MartinNohr/RadioFox/src/FoxMenus.cpp

#include "RadioFox.h"
#include "FoxMenus.h"

// do something from the menu depending on the button argument
// only two buttons are actually handled, SELECT and HELP
void RunMenus(int button)
{
    // see if we got a menu match
    bool gotmatch = false;
    int menuix = 0;
    MenuInfo *oldMenu;
    bool bExit = false;
    for (int ix = 0; !gotmatch && MenuStack.top()->menu[ix].op != eTerminate; ++ix)
    {
        // see if this is one is valid
        if (!bMenuValid[ix])
        {
            continue; // and don't increment menix
        }
        if (menuix == MenuStack.top()->index)
        {
            gotmatch = true;
            switch (button)
            {
            case BTN_B1_LONG: // handle help if there is any
                if (MenuStack.top()->menu[ix].cHelpText)
                {
                    WriteMessage(MenuStack.top()->menu[ix].cHelpText, false, -1, true);
                }
                g_bMenuChanged = true;
                break;
            case BTN_SELECT: // handle selection
                // got one, service it
                switch (MenuStack.top()->menu[ix].op)
                {
                case eTerminate: // not used, tell compiler
                case eIfEqual:
                case eIfIntEqual:
                case eElse:
                case eEndif:
                    break;
                case eText:
                case eTextInt:
                case eTextFloat:
                case eEditText:
                // case eChooseFile:
                case eBool:
                case eList:
                    g_bMenuChanged = true;
                    if (MenuStack.top()->menu[ix].change != NULL)
                    {
                        (*MenuStack.top()->menu[ix].change)(&MenuStack.top()->menu[ix], 1);
                    }
                    if (MenuStack.top()->menu[ix].function)
                    {
                        (*MenuStack.top()->menu[ix].function)(&MenuStack.top()->menu[ix]);
                    }
                    if (MenuStack.top()->menu[ix].change != NULL)
                    {
                        (*MenuStack.top()->menu[ix].change)(&MenuStack.top()->menu[ix], -1);
                    }
                    break;
                case eMenu:
                    if (MenuStack.top()->menu)
                    {
                        oldMenu = MenuStack.top();
                        MenuStack.push(new MenuInfo);
                        MenuStack.top()->menu = oldMenu->menu[ix].menu;
                        g_bMenuChanged = true;
                        MenuStack.top()->index = 0;
                        MenuStack.top()->offset = 0;
                        // Serial.println("change menu");
                    }
                    break;
                case eExit: // go back a level
                    bExit = true;
                    break;
                case eReboot:
                    WriteMessage("Rebooting in 2 seconds\nHold button for factory reset", false, 2000);
                    ESP.restart();
                    break;
                }
            }
        }
        ++menuix;
    }
    // if no match, and we are in a submenu, go back one level, or if bExit is set
    if (bExit && MenuStack.size() == 1)
    {
        g_bSettingsMode = false;
        ClearScreen();
    }
    if (bExit || (!g_bMenuChanged && MenuStack.size() > 1))
    {
        UpMenuLevel(false);
    }
}

// display the menu
// if MenuStack.top()->index is > MENU_LINES, then shift the lines up by enough to display them
// remember that we only have room for MENU_LINES lines
void ShowMenu(struct MenuItem *menu)
{
    // let the sideways scroller know that we changed the screen
    if (TaskScrollSidewaysHandle)
        xTaskNotifyGive(TaskScrollSidewaysHandle);
    MenuStack.top()->menucount = 0;
    int y = 0;
    int x = 0;
    // load with a false to start with
    std::stack<bool> skipStack;
    skipStack.push(false);
    // this is the active stack level, I.E. which level should be processed
    int skipLevel = 1;
    bool bSkipping = false;
    // loop through the menu
    for (int menix = 0; menu->op != eTerminate; ++menu, ++menix)
    {
        // make sure menu valid vector is big enough
        if (bMenuValid.size() < menix + 1)
        {
            bMenuValid.resize(menix + 1);
        }
        bMenuValid[menix] = false;
        switch ((menu->op))
        {
        case eIfEqual:
            // skip the next one if match, this is boolean only
            skipStack.push(*(bool *)menu->value != (menu->min ? true : false));
            // Serial.println("ifequal test: skip: " + String(skip));
            if (!bSkipping)
            {
                ++skipLevel;
                bSkipping = skipStack.top();
            }
            break;
        case eIfIntEqual:
            // skip the next one if match, this is int values
            skipStack.push(*(int *)menu->value != menu->min);
            // Serial.println("ifIntequal test: skip: " + String(skip));
            if (!bSkipping)
            {
                ++skipLevel;
                bSkipping = skipStack.top();
            }
            break;
        case eElse:
            skipStack.top() = !skipStack.top();
            break;
        case eEndif:
            skipStack.pop();
            if (!bSkipping || skipLevel > skipStack.size())
            {
                --skipLevel;
            }
            break;
        default:
            break;
        }
        bSkipping = skipLevel < skipStack.size() ? true : skipStack.top();
        if (bSkipping)
        {
            bMenuValid[menix] = false;
            continue;
        }
        char line[120]{}, xtraline[100]{};
        // only displayable menu items should be in this switch
        line[0] = '\0';
        int val;
        bool exists = false;
        switch (menu->op)
        {
        case eTextInt:
        case eTextFloat:
        case eText:
        case eEditText:
            // case eChooseFile:
            bMenuValid[menix] = true;
            if (menu->value)
            {
                val = *(int *)menu->value;
                if (menu->op == eText || menu->op == eEditText /*|| menu->op == eChooseFile*/)
                {
                    sprintf(line, menu->text, (char *)(menu->value));
                }
                else if (menu->op == eTextInt)
                {
                    sprintf(line, menu->text, (int)(val / pow10(menu->decimals)), val % (int)(pow10(menu->decimals)));
                }
                else if (menu->op == eTextFloat)
                {
                    double fval = *(double *)menu->value;
                    sprintf(line, menu->text, fval);
                }
            }
            else
            {
                strcpy(line, menu->text);
            }
            // next line
            ++y;
            break;
        case eList:
            bMenuValid[menix] = true;
            val = *(int *)menu->value;
            sprintf(line, menu->text, menu->nameList[val]);
            // next line
            ++y;
            break;
        case eBool:
            bMenuValid[menix] = true;
            if (menu->value)
            {
                bool *pb = (bool *)menu->value;
                sprintf(line, menu->text, *pb ? menu->on : menu->off);
            }
            else
            {
                strcpy(line, menu->text);
            }
            // increment displayable lines
            ++y;
            break;
        case eMenu:
        case eExit:
        case eReboot:
            bMenuValid[menix] = true;
            if (menu->value)
            {
                // check for %d or %s in string, be lazy and assume %s if %d not there
                if (String(menu->text).indexOf("%d") != -1)
                    sprintf(xtraline, menu->text, *(int *)menu->value);
                else
                    sprintf(xtraline, menu->text, (char *)menu->value);
            }
            else
            {
                strcpy(xtraline, menu->text);
            }
            if (menu->op == eExit)
                sprintf(line, "%s%s", "-", xtraline);
            else
                sprintf(line, "%s%s", (menu->op == eReboot) ? "" : "+", xtraline);
            ++y;
            // Serial.println("menu text4: " + String(line));
            break;
        default:
            break;
        }
        if (strlen(line) && y >= MenuStack.top()->offset)
        {
            DisplayMenuLine(y - 1, y - 1 - MenuStack.top()->offset, line);
        }
    }
    MenuStack.top()->menucount = y;
    // blank the rest of the lines
    for (int ix = y; ix < nMenuLineCount; ++ix)
    {
        DisplayLine(ix, "");
    }
    // show line if menu has been scrolled
    if (MenuStack.top()->offset > 0)
        tft.fillTriangle(0, 0, 2, 0, 0, tft.fontHeight() / 3, TFT_DARKGREY);
    // tft.drawLine(0, 0, 5, 0, menuLineActiveColor);TFT_DARKGREY
    // show bottom line if last line is showing
    if (MenuStack.top()->offset + (nMenuLineCount - 1) < MenuStack.top()->menucount - 1)
    {
        int ypos = tft.height() - 2 - tft.fontHeight() / 3;
        tft.fillTriangle(0, ypos, 2, ypos, 0, ypos - tft.fontHeight() / 3, TFT_DARKGREY);
    }
    // if (MenuStack.top()->offset + (MENU_LINES - 1) < MenuStack.top()->menucount - 1)
    //	tft.drawLine(0, tft.height() - 1, 5, tft.height() - 1, menuLineActiveColor);
    // else
    //	tft.drawLine(0, tft.height() - 1, 5, tft.height() - 1, TFT_BLACK);
    //  see if we need to clean up the end, like when the menu shrank due to a choice
    int extra = MenuStack.top()->menucount - MenuStack.top()->offset - nMenuLineCount;
    while (extra < 0)
    {
        DisplayLine(nMenuLineCount + extra, "");
        ++extra;
    }
}

// handle the menus
bool HandleMenus()
{
    if (g_bMenuChanged)
    {
        ShowMenu(MenuStack.top()->menu);
        g_bMenuChanged = false;
    }
    bool didsomething = true;
    CRotaryDialButton::Button button = ReadButton();
    int lastOffset = MenuStack.top()->offset;
    int lastMenu = MenuStack.top()->index;
    int lastMenuCount = MenuStack.top()->menucount;
    // MenuItem* pCurrentMenu = &MenuStack.top()->menu[MenuStack.top()->index];
    int btnRepeatCount = 1;
    switch (button)
    {
    case BTN_LEFT_LONG:
    case BTN_RIGHT_LONG:
        btnRepeatCount = 5;
        break;
    }
    switch (button)
    {
    case BTN_B0_CLICK: // go back a menu level if we can
        UpMenuLevel(false);
        break;
    case BTN_B1_LONG: // look for help
        // UpMenuLevel(true);	// go back to the top menu
        RunMenus(button);
        g_bMenuChanged = true;
        break;
    // case BTN_B1_LONG:
    //	button = BTN_SELECT;
    //  yes, no break here
    case BTN_SELECT:
        RunMenus(button);
        g_bMenuChanged = true;
        break;
    case BTN_RIGHT_LONG:
    case BTN_RIGHT:
        while (btnRepeatCount--)
        {
            if (SystemInfo.bAllowMenuWrap || MenuStack.top()->index < MenuStack.top()->menucount - 1)
            {
                ++MenuStack.top()->index;
            }
            if (MenuStack.top()->index >= MenuStack.top()->menucount)
            {
                MenuStack.top()->index = 0;
                g_bMenuChanged = true;
                MenuStack.top()->offset = 0;
            }
            // see if we need to scroll the menu
            if (MenuStack.top()->index - MenuStack.top()->offset > (nMenuLineCount - 1))
            {
                if (MenuStack.top()->offset < MenuStack.top()->menucount - nMenuLineCount)
                {
                    ++MenuStack.top()->offset;
                }
            }
        }
        break;
    case BTN_LEFT_LONG:
    case BTN_LEFT:
        while (btnRepeatCount--)
        {
            if (SystemInfo.bAllowMenuWrap || MenuStack.top()->index > 0)
            {
                --MenuStack.top()->index;
            }
            if (MenuStack.top()->index < 0)
            {
                MenuStack.top()->index = MenuStack.top()->menucount - 1;
                g_bMenuChanged = true;
                MenuStack.top()->offset = MenuStack.top()->menucount - nMenuLineCount;
            }
            // see if we need to adjust the offset
            if (MenuStack.top()->offset && MenuStack.top()->index < MenuStack.top()->offset)
            {
                --MenuStack.top()->offset;
            }
        }
        break;
    case BTN_LONG:
        ClearScreen();
        g_bSettingsMode = false;
        g_bMenuChanged = true;
        break;
    default:
        didsomething = false;
        break;
    }
    // check some conditions that should redraw the menu
    if (lastMenu != MenuStack.top()->index || lastOffset != MenuStack.top()->offset)
    {
        g_bMenuChanged = true;
        // Serial.println("menu changed");
    }
    return didsomething;
}

// handle keys in run mode
bool HandleRunMode()
{
    bool didsomething = true;
    int maxMenuLine = nMenuLineCount - (SystemInfo.bShowBatteryLevel ? 2 : 1);
    CRotaryDialButton::Button button = ReadButton();
    switch (button)
    {
    case BTN_SELECT:
        break;
    case BTN_RIGHT_LONG:
    case BTN_RIGHT:
        break;
    case BTN_LEFT_LONG:
    case BTN_LEFT:
        break;
    case BTN_LONG:
        g_bSettingsMode = true;
        break;
    case BTN_B0_CLICK:
        // handle on board button 0
        // toggle the run flag
        SystemInfo.bXmitEnable = !SystemInfo.bXmitEnable;
        RadioSetup(false);
        break;
    case BTN_B0_LONG:
        CancelWaitTimers(NULL);
        break;
    case BTN_B1_CLICK:
        break;
    case BTN_B1_LONG:
    case BTN_LEFT_RIGHT_LONG:
        break;
    default:
        didsomething = false;
        taskYIELD();
        break;
    }
    return didsomething;
}

// go up one menu level, return true if anything done
// set gotoMain to go all the way back to the top
bool UpMenuLevel(bool gotoMain)
{
    if (gotoMain)
    {
        while (UpMenuLevel(false))
            ;
    }
    else if (MenuStack.size() > 1)
    {
        g_bMenuChanged = true;
        menuPtr = MenuStack.top();
        MenuStack.pop();
        delete menuPtr;
        return true;
    }
    return false;
}

uint16_t ColorList[] = {
    // TFT_NAVY,
    // TFT_MAROON,
    // TFT_OLIVE,
    TFT_WHITE,
    TFT_LIGHTGREY,
    TFT_BLUE,
    TFT_SKYBLUE,
    TFT_CYAN,
    TFT_RED,
    TFT_BROWN,
    TFT_GREEN,
    TFT_MAGENTA,
    TFT_YELLOW,
    TFT_ORANGE,
    TFT_GREENYELLOW,
    TFT_GOLD,
    TFT_SILVER,
    TFT_VIOLET,
    TFT_PURPLE,
};

// find the color in the list
int FindMenuColor(uint16_t col)
{
    int ix;
    int colors = sizeof(ColorList) / sizeof(*ColorList);
    for (ix = 0; ix < colors; ++ix)
    {
        if (col == ColorList[ix])
            break;
    }
    return constrain(ix, 0, colors - 1);
}

void SetMenuColor(MenuItem *menu)
{
    bool bHiLiteColor = false;
    int maxIndex = sizeof(ColorList) / sizeof(*ColorList) - 1;
    int nTextColorIndex = FindMenuColor(SystemInfo.menuTextColor);
    int nHiLiteColorIndex = FindMenuColor(SystemInfo.menuHiLiteColor);
    int nSavedTextColorIndex = nTextColorIndex;
    int nSavedHiLiteColorIndex = nHiLiteColorIndex;
    ClearScreen();
    DisplayLine(3, "Rotate change value", SystemInfo.menuTextColor);
    DisplayLine(5, "Long B0 reset", SystemInfo.menuTextColor);
    DisplayLine(6, "Long=OK Click=Cancel", SystemInfo.menuTextColor);
    bool done = false;
    bool bChanged = true;
    int *npColor;
    String prefix0, prefix1;
    while (!done)
    {
        npColor = bHiLiteColor ? &nHiLiteColorIndex : &nTextColorIndex;
        if (bChanged)
        {
            if (bHiLiteColor)
            {
                prefix0 = "     ";
                prefix1 = "--> ";
            }
            else
            {
                prefix0 = "--> ";
                prefix1 = "     ";
            }
            DisplayLine(4, String("B0 Change to ") + (bHiLiteColor ? "Text" : "HiLite"), ColorList[nSavedTextColorIndex]);
            DisplayLine(0, prefix0 + "Text Color", SystemInfo.menuTextColor);
            DisplayLine(1, prefix1 + "HiLite Color", TFT_BLACK, SystemInfo.menuHiLiteColor);
            bChanged = false;
        }
        switch (ReadButton())
        {
        case CRotaryDialButton::BTN_LONGPRESS:
            done = true;
            break;
        case CRotaryDialButton::BTN_RIGHT:
            bChanged = true;
            if (*npColor < maxIndex)
            {
                ++(*npColor);
            }
            break;
        case CRotaryDialButton::BTN_LEFT:
            bChanged = true;
            if (*npColor > 0)
            {
                --(*npColor);
            }
            break;
        case CRotaryDialButton::BTN0_CLICK:
            bChanged = true;
            bHiLiteColor = !bHiLiteColor;
            break;
        case CRotaryDialButton::BTN0_LONGPRESS:
            nHiLiteColorIndex = nSavedHiLiteColorIndex;
            nTextColorIndex = nSavedTextColorIndex;
            bChanged = true;
            break;
        case CRotaryDialButton::BTN_CLICK:
            nHiLiteColorIndex = nSavedHiLiteColorIndex;
            nTextColorIndex = nSavedTextColorIndex;
            done = true;
            break;
        }
        SystemInfo.menuTextColor = ColorList[nTextColorIndex];
        SystemInfo.menuHiLiteColor = ColorList[nHiLiteColorIndex];
    }
}

// toggle a boolean value
void ToggleBool(MenuItem *menu)
{
    bool *pb = (bool *)menu->value;
    *pb = !*pb;
    if (menu->change != NULL)
    {
        (*menu->change)(menu, 0);
    }
    ResetTextLines();
}

// choose from one of the values, update the index and wrap around if past max
void GetSelectChoice(MenuItem *menu)
{
    int *pVal = (int *)menu->value;
    ++*pVal;
    *pVal %= menu->max + 1;
    if (menu->change != NULL)
    {
        (*menu->change)(menu, 0);
    }
    ResetTextLines();
}

// make a selection from the supplied text list in the menu
void GetSelectChoiceList(MenuItem *menu)
{
    GetSelectChoiceListHelper(menu);
}

// some people need to know if this was a cancel (simple click) return but function must be void
// return false if click for no choice, true if chosen
bool GetSelectChoiceListHelper(MenuItem *menu)
{
    bool bRetval = true;
    // holds the current selection
    int nTextIndex = *(int *)menu->value;
    int nOriginal = nTextIndex;
    // just to be safe
    if (nTextIndex < 0)
        nTextIndex = 0;
    // holds the list starting index
    int nStartIndex = nTextIndex;
    // see if we need adjust the start
    if (nTextIndex >= nMenuLineCount - 1)
    {
        nStartIndex = nTextIndex - nMenuLineCount + 2;
    }
    ClearScreen();
    DisplayLine(nMenuLineCount - 1, "Long=OK Click=Cancel", SystemInfo.menuTextColor);
    CRotaryDialButton::Button button = BTN_NONE;
    bool done = false;
    // redraw screen only when necessary
    bool bRedraw = true;
    do
    {
        if (bRedraw)
        {
            String line;
            bool hilite;
            for (int ix = 0; ix <= menu->max && ix < nMenuLineCount - 1; ++ix)
            {
                // high light the current selection
                hilite = (nTextIndex - nStartIndex) == ix;
                line = menu->nameList[ix + nStartIndex];
                if (SystemInfo.bMenuStar)
                {
                    line = (hilite ? "*" : " ") + line;
                    DisplayLine(ix, line, SystemInfo.menuTextColor);
                }
                else
                {
                    DisplayLine(ix, line, hilite ? TFT_BLACK : SystemInfo.menuTextColor, hilite ? SystemInfo.menuHiLiteColor : TFT_BLACK);
                }
            }
            bRedraw = false;
        }
        button = ReadButton();
        switch (button)
        {
        case BTN_NONE:
        case BTN_B1_CLICK:
        case BTN_B2_LONG:
        case BTN_B1_LONG:
        case BTN_B0_CLICK:
        case BTN_B0_LONG:
            break;
        case BTN_LEFT: // previous line
            if (nTextIndex > 0)
            {
                // select the previous one
                --nTextIndex;
                // check if we need to scroll
                if (nTextIndex - nStartIndex < 0)
                {
                    --nStartIndex;
                }
                bRedraw = true;
            }
            break;
        case BTN_RIGHT: // next line
            // check if more available
            if (nTextIndex < menu->max)
            {
                ++nTextIndex;
                // check if we need to scroll
                if (nTextIndex - nStartIndex >= nMenuLineCount - 1)
                {
                    ++nStartIndex;
                }
                bRedraw = true;
            }
            break;
        case BTN_LONG: // set the new index
            *(int *)menu->value = nTextIndex;
            done = true;
            bRetval = true;
            break;
        case BTN_SELECT: // use this to cancel and return original value
            *(int *)menu->value = nOriginal;
            done = true;
            bRetval = false;
            break;
        }
    } while (!done);
    ResetTextLines();
    return bRetval;
}

// get integer values
void GetIntegerValue(MenuItem *menu)
{
    ClearScreen();
    // -1 means to reset to original
    int stepSize = 1;
    int originalValue = *(int *)menu->value;
    // Serial.println("int: " + String(menu->text) + String(*(int*)menu->value));
    char line[50];
    CRotaryDialButton::Button button = BTN_NONE;
    bool done = false;
    const char *fmt;
    if (menu->decimals)
    {
        static char fmtInfo[50];
        // String st = String("%ld.%0") + menu->decimals + "ld";
        sprintf(fmtInfo, "%%ld.%%0%dld", menu->decimals);
        fmt = fmtInfo;
    }
    else
    {
        fmt = "%ld";
    }
    char minstr[50], maxstr[50], valstr[50];
    sprintf(line, menu->text, *(int *)menu->value / (int)pow10(menu->decimals), *(int *)menu->value % (int)pow10(menu->decimals));
    DisplayLine(0, line, SystemInfo.menuTextColor);
    sprintf(minstr, fmt, menu->min / (int)pow10(menu->decimals), abs(menu->min % (int)pow10(menu->decimals)));
    sprintf(maxstr, fmt, menu->max / (int)pow10(menu->decimals), abs(menu->max % (int)pow10(menu->decimals)));
    DisplayLine(1, String(minstr) + " to " + String(maxstr), SystemInfo.menuTextColor);
    DisplayLine(5, "Long Press B0 to reset", SystemInfo.menuTextColor);
    DisplayLine(6, "Long Press to Accept", SystemInfo.menuTextColor);
    int oldVal = *(int *)menu->value;
    bool bChange = true;
    do
    {
        if (bChange)
        {
            // make sure within limits
            *(int *)menu->value = constrain(*(int *)menu->value, menu->min, menu->max);
            // show slider bar
            tft.fillRect(0, 2 * tft.fontHeight(), tft.width() - 1, 6, TFT_BLACK);
            DrawProgressBar(0, 2 * tft.fontHeight() + 4, tft.width() - 1, 12, map(*(int *)menu->value, menu->min, menu->max, 0, 100), true);
            sprintf(valstr, fmt, *(int *)menu->value / (int)pow10(menu->decimals), abs(*(int *)menu->value % (int)pow10(menu->decimals)));
            DisplayLine(3, String("New Value: ") + valstr, SystemInfo.menuTextColor);
            sprintf(valstr, fmt, stepSize / (int)pow10(menu->decimals), stepSize % (int)pow10(menu->decimals));
            DisplayLine(4, stepSize == -1 ? "Reset: long press (Click +)" : "Step: " + String(valstr) + " (Click +)", SystemInfo.menuTextColor);
            if (menu->change != NULL && oldVal != *(int *)menu->value)
            {
                (*menu->change)(menu, 0);
                oldVal = *(int *)menu->value;
            }
            bChange = false;
        }
        button = ReadButton();
        switch (button)
        {
        case BTN_LEFT:
            if (stepSize != -1)
                *(int *)menu->value -= stepSize;
            break;
        case BTN_RIGHT:
            if (stepSize != -1)
                *(int *)menu->value += stepSize;
            break;
        case BTN_SELECT:
        case BTN_B0_CLICK:
            if (stepSize == -1)
            {
                stepSize = 1;
            }
            else
            {
                stepSize *= 10;
            }
            if (stepSize > (menu->max / 2))
            {
                stepSize = -1;
            }
            break;
        case BTN_B0_LONG: // reset
            *(int *)menu->value = originalValue;
            stepSize = 1;
            break;
        case BTN_LONG:
            if (stepSize == -1)
            {
                *(int *)menu->value = originalValue;
                stepSize = 1;
            }
            else
            {
                done = true;
            }
            break;
        }
        bChange = (button != BTN_NONE);
    } while (!done);
}

// get double float values
void GetFloatValue(MenuItem *menu)
{
    ClearScreen();
    // -1 means to reset to original
    int stepSize = 0;
    double originalValue = *(double *)menu->value;
    // Serial.println("int: " + String(menu->text) + String(*(int*)menu->value));
    char line[50];
    CRotaryDialButton::Button button = BTN_NONE;
    bool done = false;
    const char *fmt;
    static char fmtInfo[50];
    sprintf(fmtInfo, "%%.%df", menu->decimals);
    fmt = fmtInfo;
    char minstr[50], maxstr[50], valstr[50];
    sprintf(line, menu->text, *(double *)menu->value);
    DisplayLine(0, line, SystemInfo.menuTextColor);
    sprintf(minstr, fmt, menu->fmin);
    sprintf(maxstr, fmt, menu->fmax);
    DisplayLine(1, String(minstr) + " to " + String(maxstr), SystemInfo.menuTextColor);
    DisplayLine(5, "Long Press B0 to reset", SystemInfo.menuTextColor);
    DisplayLine(6, "Long Press to Accept", SystemInfo.menuTextColor);
    double oldVal = *(double *)menu->value;
    bool bChange = true;
    do
    {
        if (bChange)
        {
            // make sure within limits
            *(double *)menu->value = constrain(*(double *)menu->value, menu->fmin, menu->fmax);
            // show slider bar
            tft.fillRect(0, 2 * tft.fontHeight(), tft.width() - 1, 6, TFT_BLACK);
            long pc = map(*(double *)menu->value, menu->fmin, menu->fmax, 0, 100);
            DrawProgressBar(0, 2 * tft.fontHeight() + 4, tft.width() - 1, 12, pc, true);
            sprintf(valstr, fmt, *(double *)menu->value);
            DisplayLine(3, String("New Value: ") + valstr, SystemInfo.menuTextColor);
            sprintf(valstr, fmt, pow10(stepSize - menu->decimals));
            DisplayLine(4, stepSize == -1 ? "Reset: long press (Click +)" : "Step: " + String(valstr) + " (Click +)", SystemInfo.menuTextColor);
            if (menu->change != NULL && oldVal != *(double *)menu->value)
            {
                (*menu->change)(menu, 0);
                oldVal = *(double *)menu->value;
            }
            bChange = false;
        }
        button = ReadButton();
        switch (button)
        {
        case BTN_LEFT:
            if (stepSize != -1)
                *(double *)menu->value -= pow10(stepSize - menu->decimals);
            break;
        case BTN_RIGHT:
            if (stepSize != -1)
                *(double *)menu->value += pow10(stepSize - menu->decimals);
            break;
        case BTN_SELECT:
        case BTN_B0_CLICK:
            ++stepSize;
            if (stepSize > log10(menu->fmax) + menu->decimals)
            {
                stepSize = -1;
            }
            break;
        case BTN_B0_LONG: // reset
            *(double *)menu->value = originalValue;
            stepSize = 1;
            break;
        case BTN_LONG:
            if (stepSize == -1)
            {
                *(double *)menu->value = originalValue;
                stepSize = 1;
            }
            else
            {
                done = true;
            }
            break;
        }
        bChange = (button != BTN_NONE);
    } while (!done);
}

// handle the dial and menu system
// also check for some system settings changes and deal with them, e.g. radio settings
void TaskMenu(void *params)
{
    static SYSTEM_INFO SystemInfoSaved;
    static BATTERY_INFO BatteryInfoSaved;
    static bool bLastSettingsMode = false;
    for (;;)
    {
        if (g_bSettingsMode)
        {
            HandleMenus();
            // check for some conditions that must be adjusted
            if (SystemInfo.bBeaconMode)
            {
                // only certain frequencies are allowed in Beacon mode
                if (SystemInfo.nFrequency < BEACON_LOW_FREQUENCY || SystemInfo.nFrequency > BEACON_HIGH_FREQUENCY)
                {
                    SystemInfo.nFrequency = BEACON_LOW_FREQUENCY;
                }
            }
            // if beacon mode off, make sure the send GPS flag is off
            if (!SystemInfo.bBeaconMode)
            {
                SystemInfo.bSendGPS = false;
            }
        }
        else
        {
            HandleRunMode();
        }
        // did settings mode just turn on?
        if (g_bSettingsMode && !bLastSettingsMode)
        {
            memcpy(&SystemInfoSaved, &SystemInfo, sizeof(SystemInfo));
            memcpy(&BatteryInfoSaved, &BatteryInfo, sizeof(BatteryInfo));
            ClearScreen();
        }
        // did settings mode just turn off?
        if (!g_bSettingsMode && bLastSettingsMode)
        {
            // show the battery display by telling the task to run
            xTaskNotifyGive(TaskShowBatteryHandle);
            if (memcmp(&SystemInfoSaved, &SystemInfo, sizeof(SystemInfo)) || memcmp(&BatteryInfoSaved, &BatteryInfo, sizeof(BatteryInfo)))
            {
                // make sure that the lcd dim is less than the bright
                if (SystemInfo.nDisplayDimValue > SystemInfo.nDisplayBrightness)
                    SystemInfo.nDisplayDimValue = SystemInfo.nDisplayBrightness;
                // figure out if any radio settings need to be sent to the radio
                bool bRadioChanges = false;
                // scan the important settings
                bRadioChanges = CompareRadioSettings(&SystemInfo, &SystemInfoSaved);
                // tell the radio
                if (RadioSetup(bRadioChanges))
                {
                    // worked
                }
                else
                {
                    // TODO failed, turn off transmit?
                }
                // copy so we know we updated things
                memcpy(&SystemInfoSaved, &SystemInfo, sizeof(SystemInfo));
                memcpy(&BatteryInfoSaved, &BatteryInfo, sizeof(BatteryInfo));
                SaveLoadSettings(true, false);
            }
        }
        bLastSettingsMode = g_bSettingsMode;
        vTaskDelay(pdMS_TO_TICKS(2));
        // int freestack = uxTaskGetStackHighWaterMark(NULL);
        // Serial.println(String("menu high water: ") + freestack);
    }
}

// get a yes/no response
bool GetYesNo(String msg)
{
    int pad = tft.getTextPadding();
    tft.setTextPadding(0);
    bool retval = false;
    bool change = true;
    ClearScreen();
    DisplayLine(1, msg, SystemInfo.menuTextColor);
    DisplayLine(4, "Rotate to Change", SystemInfo.menuTextColor);
    DisplayLine(5, "Click to Select", SystemInfo.menuTextColor);
    CRotaryDialButton::Button button = BTN_NONE;
    bool done = false;
    while (!done)
    {
        button = ReadButton();
        switch (button)
        {
        case BTN_LEFT:
        case BTN_RIGHT:
            retval = !retval;
            change = true;
            break;
        case BTN_SELECT:
            // case BTN_LONG:
            done = true;
            break;
        default:
            break;
        }
        if (change)
        {
            // draw the buttons
            tft.fillRoundRect(60, 42, 60, 22, 8, SystemInfo.menuTextColor);
            tft.setTextColor(TFT_BLACK, SystemInfo.menuTextColor);
            tft.drawString(retval ? "Yes" : "No", 72, 46);
            change = false;
        }
    }
    tft.setTextPadding(pad);
    return retval;
}

void ResetDimTimer()
{
    displayDimTimer = SystemInfo.nDisplayDimTime;
    if (SystemInfo.eDisplayDimMode == DISPLAY_DIM_MODE_TIME && SystemInfo.nDisplayDimTime)
    {
        SetDisplayBrightness(SystemInfo.nDisplayBrightness);
    }
}

void UpdateDisplayBrightness(MenuItem *menu, int flag)
{
    // control LCD brightness
    SetDisplayBrightness(*(int *)menu->value);
}

void UpdateDisplayDimMode(MenuItem *menu, int flag)
{
    switch (flag)
    {
    case 0: // first time
        break;
    case 1: // every change
        break;
    case -1: // last time
        SetDisplayBrightness(SystemInfo.nDisplayBrightness);
    }
}

void SetDisplayBrightness(int val)
{
    ledcWrite(TFT_ENABLE, map(val, 0, 100, 0, 255));
}

// display a line in selected colors and clear to the end of the line
void DisplayLine(int lineNum, String text, uint16_t color, uint16_t backColor)
{
    if (xSemaphoreTake(MutexDisplayHandle, portMAX_DELAY) == pdTRUE)
    {
        if (lineNum >= 0 && lineNum < nMenuLineCount)
        {
            if (TextLines[lineNum].Line != text || TextLines[lineNum].backColor != backColor || TextLines[lineNum].foreColor != color)
            {
                int pixels = tft.textWidth(text);
                if (pixels > tft.width())
                {
                    TextLines[lineNum].nRollLength = pixels;
                    TextLines[lineNum].nRollOffset = 0;
                }
                else
                {
                    TextLines[lineNum].nRollOffset = TextLines[lineNum].nRollLength = 0;
                }
                // save the line for scrolling purposes
                TextLines[lineNum].Line = text;
                TextLines[lineNum].foreColor = color;
                TextLines[lineNum].backColor = backColor;
            }
            // push the sprite text to the display
            int y = lineNum * tft.fontHeight();
            LineSprite.setTextColor(color, backColor);
            LineSprite.drawString(text, -TextLines[lineNum].nRollOffset, 0);
            LineSprite.pushSprite(0, y);
        }
        xSemaphoreGive(MutexDisplayHandle);
    }
}

// clear the screen and reset the scrolling lines
void ClearScreen()
{
    if (xSemaphoreTake(MutexDisplayHandle, portMAX_DELAY) == pdTRUE)
    {
        // let the sideways scroller know that we cleared the screen
        if (TaskScrollSidewaysHandle)
            xTaskNotifyGive(TaskScrollSidewaysHandle);
        tft.fillScreen(TFT_BLACK);
        ResetTextLines();
        xSemaphoreGive(MutexDisplayHandle);
    }
}

void ResetTextLines()
{
    for (int ix = 0; ix < nMenuLineCount; ++ix)
    {
        TextLines[ix].Line.clear();
        TextLines[ix].nRollOffset = 0;
        TextLines[ix].nRollLength = 0;
        TextLines[ix].foreColor = 0;
        TextLines[ix].backColor = 0;
        TextLines[ix].nRollDirection = 0;
    }
}

// active menu line is in reverse video or * at front depending on bMenuStar
void DisplayMenuLine(int lineNum, int displine, String text)
{
    bool hilite = MenuStack.top()->index == lineNum;
    String mline = (hilite && SystemInfo.bMenuStar ? "*" : " ") + text;
    if (displine >= 0 && displine < nMenuLineCount)
    {
        if (SystemInfo.bMenuStar)
        {
            DisplayLine(displine, mline, SystemInfo.menuTextColor, TFT_BLACK);
        }
        else
        {
            DisplayLine(displine, mline, hilite ? TFT_BLACK : SystemInfo.menuTextColor, hilite ? SystemInfo.menuHiLiteColor : TFT_BLACK);
        }
    }
}

// insert newlines into a string so it doesn't wrap in the middle of words when displayed
// existing newlines are honored
String FormatMultiLine(String &input)
{
    String output;
    int lineWidth = 0;
    int lastInputSpace = 0;
    int lastOutputSpace = 0;
    int lastOutputStart = 0;
    // look for spaces and add words to the output, when each line is too long start a new line
    for (int inIx = 0; inIx < input.length(); ++inIx)
    {
        switch (input[inIx])
        {
        case '\n':
            // flush the line
            output += '\n';
            lastOutputStart = output.length();
            break;
        case ' ':
            output += input[inIx];
            // mark the space location so we can go back
            lastInputSpace = inIx;
            lastOutputSpace = output.length();
            break;
        default:
            // check the width after adding this character
            output += input[inIx];
            lineWidth = tft.textWidth(output.substring(lastOutputStart));
            if (lineWidth > tft.width())
            {
                // too wide, backup
                output = output.substring(0, lastOutputSpace);
                // add a newline to the output
                output += '\n';
                inIx = lastInputSpace;
                lastOutputStart = output.length();
            }
            break;
        }
    }
    return output;
}

// display message on first line, if wait is -1, wait for a key press
void WriteMessage(String txt, bool error, int wait, bool process)
{
    ClearScreen();
    if (xSemaphoreTake(MutexDisplayHandle, portMAX_DELAY) == pdTRUE)
    {
        if (process)
        {
            txt = FormatMultiLine(txt);
        }
        if (error)
        {
            txt = "**" + txt + "**";
            tft.setTextColor(TFT_RED);
        }
        else
        {
            tft.setTextColor(SystemInfo.menuTextColor);
        }
        tft.setCursor(0, tft.fontHeight());
        tft.setTextWrap(true);
        tft.print(txt);
        if (wait == -1)
        {
            // wait for a key
            while (ReadButton() == BTN_NONE)
                delay(10);
        }
        else
        {
            delay(wait);
        }
        tft.setTextColor(TFT_WHITE);
        xSemaphoreGive(MutexDisplayHandle);
    }
    // ClearScreen();
}

// compare strings for sort ignoring case
bool CompareNames(const String &a, const String &b)
{
    String a1 = a, b1 = b;
    a1.toUpperCase();
    b1.toUpperCase();
    return a1.compareTo(b1) < 0;
}

#define MAX_SETTINGS_NAME_LENGTH 13
// get a filename from the user to save the settings in
String GetFilename()
{
    static String text = "";
    ClearScreen();
    String letters = "ABCDEFGHIJKLMNOPQRSTUVWXYZ0123456789-_$#()@";
    CRotaryDialButton::Button button = BTN_NONE;
    bool done = false;
    DisplayLine(5, "Rotate dial to select, Click appends char", SystemInfo.menuTextColor);
    DisplayLine(6, "Long press dial exits, B0 deletes last char, B0 Long clears text", SystemInfo.menuTextColor);
    int nLetterIndex = 0;
    // redraw screen only when necessary
    bool bRedraw = true;
    const int partA = 18; // first line
    do
    {
        if (bRedraw)
        {
            DisplayLine(0, text, SystemInfo.menuTextColor);
            // draw the text
            DisplayLine(1, letters.substring(0, partA), SystemInfo.menuTextColor);
            DisplayLine(2, letters.substring(partA, partA * 2), SystemInfo.menuTextColor);
            DisplayLine(3, letters.substring(partA * 2), SystemInfo.menuTextColor);
            // figure out which letter to hilite
            int y = nLetterIndex / partA;
            y = constrain(y, 0, 2);
            int x = tft.textWidth(letters.substring(y * partA, nLetterIndex));
            char ch[2] = {0};
            ch[0] = letters[nLetterIndex];
            if (SystemInfo.bMenuStar)
            {
                tft.drawChar(x + 1, tft.fontHeight() * (y + 2) - 6, letters[nLetterIndex], TFT_WHITE, TFT_BLACK, 1);
            }
            else
            {
                tft.fillRect(x + 1, tft.fontHeight() * (y + 1) - 4, tft.textWidth(ch), (y + 2) + tft.fontHeight(), SystemInfo.menuTextColor);
                tft.drawChar(x + 1, tft.fontHeight() * (y + 2) - 6, letters[nLetterIndex], TFT_BLACK, TFT_BLACK, 1);
            }
            bRedraw = false;
        }
        button = ReadButton();
        switch (button)
        {
        case BTN_NONE:
        case BTN_B1_CLICK:
        case BTN_B2_LONG:
        case BTN_B1_LONG:
            break;
        case BTN_LEFT:
            if (nLetterIndex)
                --nLetterIndex;
            else
                nLetterIndex = letters.length() - 1;
            bRedraw = true;
            break;
        case BTN_RIGHT:
            if (nLetterIndex < letters.length() - 1)
                ++nLetterIndex;
            else
                nLetterIndex = 0;
            bRedraw = true;
            break;
        case BTN_SELECT: // add a letter if room
            if (text.length() < MAX_SETTINGS_NAME_LENGTH)
            {
                text += letters[nLetterIndex];
                bRedraw = true;
            }
            break;
        case BTN_B0_CLICK: // delete last character
            if (text.length())
                text = text.substring(0, text.length() - 1);
            bRedraw = true;
            break;
        case BTN_B0_LONG: // clear the text
            text.clear();
            bRedraw = true;
            break;
        case BTN_LONG:
            done = true;
            break;
        }
    } while (!done);
    return text;
}

// get the name from the SD list
String GetSettingsFilename()
{
    int index = 0;
    std::vector<String> namelist;
    GetFileNamesFromSD(namelist, false, "RFS");
    if (namelist.size() == 0)
    {
        WriteMessage("No saved settings");
        return "";
    }
    const char **list;
    list = (const char **)calloc(sizeof(char *), namelist.size());
    if (list == NULL)
    {
        WriteMessage("failed to alloc file list", true);
        return "";
    }

    for (int ix = 0; ix < namelist.size(); ++ix)
    {
        // remove the extension
        namelist[ix] = namelist[ix].substring(0, namelist[ix].length() - 4);
        list[ix] = namelist[ix].c_str();
    }
    MenuItem mi = {eList, "File: %s", GetSelectChoice, &index, 0, (long)namelist.size() - 1, 0, NULL, NULL, NULL, list};
    bool bChosen = GetSelectChoiceListHelper(&mi);
    free(list);
    return bChosen ? namelist[index] : "";
}

// create and save the settings in a named file
void CreateSettingsFile(MenuItem *)
{
    // get the filename
    String fname = GetFilename();
    if (fname.length() == 0)
    {
        WriteMessage("no file saved");
        return;
    }
    // open the file and save the settings
    File binFile;
    // first check if the file exists
    if (SD.exists("/" + fname + ".RFS") && !GetYesNo("Replace\n" + fname + "?"))
    {
        WriteMessage(fname + "\nnot changed");
        return;
    }
    // if we get here, write the file
    binFile = SD.open("/" + fname + ".RFS", FILE_WRITE, true);
    if (binFile)
    {
        binFile.write((uint8_t *)&SystemInfo, sizeof(SystemInfo));
        binFile.close();
        WriteMessage(fname + "\nsaved");
    }
    else
    {
        WriteMessage(fname + "\nnot saved");
    }
}

// Save or update the settings in a named file
void SaveSettingsInFile(MenuItem *)
{
    // get the filename
    String fname = GetSettingsFilename();
    if (fname.length() == 0)
    {
        WriteMessage("no file saved");
        return;
    }
    // open the file and save the settings
    File binFile;
    // first check if the file exists
    if (SD.exists("/" + fname + ".RFS") && !GetYesNo("Replace\n" + fname + "?"))
    {
        WriteMessage(fname + "\nnot changed");
        return;
    }
    // if we get here, write the file
    binFile = SD.open("/" + fname + ".RFS", FILE_WRITE, true);
    if (binFile)
    {
        binFile.write((uint8_t *)&SystemInfo, sizeof(SystemInfo));
        binFile.close();
        WriteMessage(fname + "\nsaved");
    }
    else
    {
        WriteMessage(fname + "\nnot saved");
    }
}

// load the settings from a named file
void LoadSettingsFromFile(MenuItem *)
{
    File file;
    String fname = GetSettingsFilename();
    if (fname.length())
    {
        if ((file = SD.open(String("/") + fname + ".RFS", FILE_READ)))
        {
            file.read((uint8_t *)&SystemInfo, sizeof(SystemInfo));
            file.close();
            WriteMessage(fname + "\nloaded");
        }
        else
        {
            WriteMessage(fname + "\nnot loaded");
        }
    }
    else
    {
        WriteMessage("no file selected");
    }
}

// Delete a settings file
void DeleteSettingsFile(MenuItem *)
{
    String fname = GetSettingsFilename();
    String fullname = "/" + fname + ".RFS";
    if (fname.length())
    {
        if (SD.exists(fullname))
        {
            if (GetYesNo("delete: \n" + fname))
            {
                SD.remove(fullname);
                WriteMessage(fname + "\ndeleted");
            }
            else
            {
                WriteMessage(fname + "\nnot deleted");
            }
        }
    }
    else
    {
        WriteMessage("no file selected");
    }
}

// save the eeprom settings
void SaveEepromSettings(MenuItem *menu)
{
    SaveLoadSettings(true, false);
}

//// load eeprom settings
// void LoadEepromSettings(MenuItem * menu)
//{
//	SaveLoadSettings(false, false);
// }

// draw a progress bar
void DrawProgressBar(int x, int y, int dx, int dy, int percent, bool rect)
{
    if (xSemaphoreTake(MutexDisplayHandle, portMAX_DELAY) == pdTRUE)
    {
        if (rect)
            tft.drawRoundRect(x, y, dx, dy, 2, SystemInfo.menuTextColor);
        int fill = (dx - 2) * percent / 100;
        // fill the filled part
        tft.fillRect(x + 1, y + 1, fill, dy - 2, TFT_DARKGREEN);
        // blank the empty part
        tft.fillRect(x + 1 + fill, y + 1, dx - 2 - fill, dy - 2, TFT_BLACK);
        xSemaphoreGive(MutexDisplayHandle);
    }
}

// read the battery level, LiIon cells are 4.2 fully charged and should not be discharged below 2.75 (some say 3.2)
// smoothing of the reading is done using an exponential moving average
int ReadBattery(int *raw)
{
    static bool bFirstTime = true;
    const float alpha = 0.9;
    static float eSmooth = 0.0;
    int percent;
    float nextLevel;
    // take extra passes the first time to read a more accurate value
    for (int tries = 0; tries < (bFirstTime ? 50 : 5); ++tries)
    {
        nextLevel = (float)analogRead(BATTERY_SENSOR_GPIO);
        // calculate the next value
        eSmooth = (alpha * eSmooth) + ((1 - alpha) * nextLevel);
        // calculate the %
        if (eSmooth >= BatteryInfo.nBatteryFullLevel)
            percent = 100;
        else if (eSmooth <= LOW_BATTERY_VALUE)
            percent = 0;
        else
        {
            percent = (eSmooth - LOW_BATTERY_VALUE) * 100 / (BatteryInfo.nBatteryFullLevel - LOW_BATTERY_VALUE);
        }
        vTaskDelay(pdMS_TO_TICKS(2));
    }
    bFirstTime = false;
    if (raw)
        *raw = (int)eSmooth;
    if (percent == 0)
    {
        static int count0 = 0;
        // we need at least 5 0's before claiming no power, it takes a few cycles to stabilize
        if (count0++ > 5)
        {
            SystemInfo.bCriticalBatteryLevel = true;
        }
    }
    return percent;
}

//// reset the battery indicator, this is done by setting it to 1/2 and letting the ShowBattery code letting it rise to its maximum level
// void ResetBattery(MenuItem* menu)
//{
//	if (GetYesNo("Reset Battery Calibration?")) {
//		WriteMessage("Calibration reset,\nfully charge battery\nto finish", false, 5000);
//		SystemInfo.nBatteryFullLevel /= 2;
//	}
// }

// this code shows the battery on the main display when menu is NULL
// otherwise it shows the current raw integer readings of the battery sensor
// if this call comes from the menu system the display is already locked, otherwise we lock it here
void ShowBattery(MenuItem *menu)
{
    static int percent = 0, raw = 0;
    if (menu)
        ClearScreen();
    static unsigned long showtime = 0;
    while (!menu || ReadButton() != BTN_LONG)
    {
        percent = ReadBattery(&raw);
        if (millis() > showtime + 1000)
        {
            if (menu)
            {
                DisplayLine(0, "Battery: " + String(percent) + "%", SystemInfo.menuTextColor);
                DisplayLine(1, "Raw Battery: " + String(raw), SystemInfo.menuTextColor);
                DisplayLine(3, "Long Press to Cancel", SystemInfo.menuTextColor);
            }
            else
            {
                // update the battery calibration by setting the max value to 90% of what is read when it is larger than the last value
                if (xSemaphoreTake(MutexDisplayHandle, portMAX_DELAY) == pdTRUE)
                {
                    // TODO: fix this so it works for a sprite that is not 100 pixels wide
                    int sh = BatterySprite.height();
                    BatterySprite.fillSprite(TFT_BLACK);
                    BatterySprite.setTextColor(SystemInfo.menuTextColor);
                    // show % full
                    BatterySprite.fillRect(0, sh - BATTERY_BAR_HEIGHT - 2, percent, BATTERY_BAR_HEIGHT, SystemInfo.menuTextColor);
                    // thin line rest of line
                    BatterySprite.fillRect(percent, sh - 4, 100 - percent, 2, SystemInfo.menuTextColor);
                    // show the text above the bar
                    String pc = "Bat: " + String(percent) + "%";
                    BatterySprite.drawString(pc, 100 - tft.textWidth(pc) - 2, 0);
                    // push the sprite to the display
                    BatterySprite.pushSprite(tft.width() - 101, tft.height() - sh + 2);
                    xSemaphoreGive(MutexDisplayHandle);
                    //// see if this value is larger than the current calibration, use 90% of value during charging
                    // int rawNew = raw * 0.90;
                    // if (rawNew > SystemInfo.nBatteryFullLevel) {
                    //	//Serial.println(String("full: ") + SystemInfo.nBatteryFullLevel + " raw: " + raw + " read: " + rawNew);
                    //	SystemInfo.nBatteryFullLevel = rawNew;
                    //	BatteryInfo.nBatteryLowLevel = rawNew * 3.2 / 4.2;
                    //	SaveLoadSettings(true, true);
                    // }
                }
            }
            showtime = millis();
        }
        if (menu)
            delay(100);
        else
            break;
    }
}

//// set the low battery level from the current value
// void SetLowBattery(MenuItem*)
//{
//	ReadBattery(&BatteryInfo.nBatteryLowLevel);
// }

// set the high battery level from the current value
void SetHighBattery(MenuItem *)
{
    ReadBattery(&BatteryInfo.nBatteryFullLevel);
}

void ShowProgressBar(int percent)
{
    static int lastpercent = 0;
    if (lastpercent && (lastpercent == percent))
        return;
    int x = tft.width() - 1;
    int y = (tft.fontHeight() + 4);
    int h = 8;
    if (percent == 0)
    {
        if (xSemaphoreTake(MutexDisplayHandle, portMAX_DELAY) == pdTRUE)
        {
            tft.fillRect(0, y, x, h, TFT_BLACK);
            xSemaphoreGive(MutexDisplayHandle);
        }
    }
    DrawProgressBar(0, y, x, h, percent, true);
    lastpercent = percent;
}

// show the update bin file progress
void ShowUpdateProgress(size_t x, size_t total)
{
    ShowProgressBar(x * 100 / total);
}

// see if there is an update bin file in the SD slot
void CheckUpdateBin(MenuItem *menu)
{
    // const char* binFileName = "/RadioFox.ino.ttgo-t1.bin";
    const char *binFileName = "/RadioFox.bin";
    if (SD.exists(binFileName))
    {
        if (GetYesNo("Load New Firmware?"))
        {
            ClearScreen();
            DisplayLine(2, "loading...");
            File binFile;
            binFile = SD.open(binFileName);
            if (binFile)
            {
                size_t binSize = binFile.size();
                Update.begin(binSize, U_FLASH);
                Update.onProgress(ShowUpdateProgress);
                size_t bytesWritten = Update.writeStream(binFile);
                Update.end();
                binFile.close();
                ClearScreen();
                if (GetYesNo("Delete BIN file?"))
                {
                    SD.remove(binFileName);
                }
                ClearScreen();
                ESP.restart();
            }
        }
    }
    else
    {
        WriteMessage(String("No: ") + binFileName, true);
    }
}

// choose a network name from the first 5 found
void GetNetworkName(MenuItem *menu)
{
    ClearScreen();
    DisplayLine(0, "Scanning Networks...", SystemInfo.menuTextColor, TFT_BLACK);
    int nets = ScanForNetworks();
    // maximum 5 nets
    constexpr int maxNetworks = 5;
    nets = min(nets, maxNetworks);
    for (int ix = 0; ix < nets; ++ix)
    {
        DisplayLine(ix, WiFi.SSID(ix), SystemInfo.menuTextColor, TFT_BLACK);
    }
    // loop handling key presses
    int which = 0;
    bool done = false;
    DisplayLine(6, "Longpress=accept LongB0=cancel", SystemInfo.menuTextColor, TFT_BLACK);
    DisplayLine(which, WiFi.SSID(which), TFT_BLACK, SystemInfo.menuTextColor);
    while (!done)
    {
        CRotaryDialButton::Button btn = ReadButton();
        switch (btn)
        {
        case CRotaryDialButton::BTN_LONGPRESS:
            strncpy((char *)menu->value, WiFi.SSID(which).c_str(), menu->max - 1);
            bControllerReboot = true;
            done = true;
            break;
        case CRotaryDialButton::BTN0_LONGPRESS:
            done = true;
            break;
        case CRotaryDialButton::BTN_RIGHT:
            if (which < maxNetworks - 1)
            {
                DisplayLine(which, WiFi.SSID(which), SystemInfo.menuTextColor, TFT_BLACK);
                ++which;
                DisplayLine(which, WiFi.SSID(which), TFT_BLACK, SystemInfo.menuTextColor);
            }
            break;
        case CRotaryDialButton::BTN_LEFT:
            if (which > 0)
            {
                DisplayLine(which, WiFi.SSID(which), SystemInfo.menuTextColor, TFT_BLACK);
                --which;
                DisplayLine(which, WiFi.SSID(which), TFT_BLACK, SystemInfo.menuTextColor);
            }
            break;
        default:
            break;
        }
    }
    delay(10);
}

// get the text from a menu item
void GetText(MenuItem *menu)
{
    char *str = (char *)menu->value;
    if (str)
    {
        String text = str;
        ClearScreen();
        String upperLetters = "ABCDEFGHIJKLMNOPQRSTUVWXYZ0123456789 -_@#$%^&|";
        String lowerLetters = "abcdefghijklmnopqrstuvwxyz0123456789 -_@#$%^&|";
        String letters = upperLetters;
        bool bUpper = true;
        CRotaryDialButton::Button button = BTN_NONE;
        bool done = false;
        if (menu->op == eBool)
        {
            DisplayLine(5, "Rotate dial to select, Click appends char, '|' separates OR fields", SystemInfo.menuTextColor);
            DisplayLine(6, "Long press dial exits, B0 deletes last char, B0 Long clears text", SystemInfo.menuTextColor);
        }
        else
        {
            DisplayLine(5, "Rotate dial to select, Click appends char, B1 Long toggles case", SystemInfo.menuTextColor);
            DisplayLine(6, "Long press dial exits, B0 deletes last char, B0 Long clears text", SystemInfo.menuTextColor);
        }
        int nLetterIndex = 0;
        // redraw screen only when necessary
        bool bRedraw = true;
        const int partA = 13; // half the alphabet
        do
        {
            if (bRedraw)
            {
                DisplayLine(0, text, SystemInfo.menuTextColor);
                // draw the text
                DisplayLine(1, letters.substring(0, partA), SystemInfo.menuTextColor);
                DisplayLine(2, letters.substring(partA, partA * 2), SystemInfo.menuTextColor);
                DisplayLine(3, letters.substring(partA * 2), SystemInfo.menuTextColor);
                // figure out which letter to hilite
                int y = nLetterIndex / partA;
                y = constrain(y, 0, 2);
                int x = tft.textWidth(letters.substring(y * partA, nLetterIndex));
                char ch[2] = {0};
                ch[0] = letters[nLetterIndex];
                // the width calculation for ' ' is 0 (an error!), so we use something close
                if (ch[0] == ' ')
                    ch[0] = '|';
                if (SystemInfo.bMenuStar)
                {
                    tft.drawChar(x + 1, tft.fontHeight() * (y + 2) - 6, letters[nLetterIndex], TFT_WHITE, TFT_BLACK, 1);
                }
                else
                {
                    tft.fillRect(x + 1, tft.fontHeight() * (y + 1) - 4, tft.textWidth(ch), (y + 2) + tft.fontHeight(), SystemInfo.menuTextColor);
                    tft.drawChar(x + 1, tft.fontHeight() * (y + 2) - 6, letters[nLetterIndex], TFT_BLACK, TFT_BLACK, 1);
                }
                bRedraw = false;
            }
            button = ReadButton();
            switch (button)
            {
            case BTN_NONE:
            case BTN_B1_CLICK:
            case BTN_B2_LONG:
                break;
            case BTN_B1_LONG:
                if (menu->op != eBool)
                {
                    bUpper = !bUpper;
                    letters = bUpper ? upperLetters : lowerLetters;
                    bRedraw = true;
                }
                break;
            case BTN_LEFT:
                if (nLetterIndex)
                    --nLetterIndex;
                else
                    nLetterIndex = letters.length() - 1;
                bRedraw = true;
                break;
            case BTN_RIGHT:
                if (nLetterIndex < letters.length() - 1)
                    ++nLetterIndex;
                else
                    nLetterIndex = 0;
                bRedraw = true;
                break;
            case BTN_SELECT: // add a letter if room
                if (text.length() < menu->max)
                {
                    text += letters[nLetterIndex];
                    bRedraw = true;
                }
                break;
            case BTN_B0_CLICK: // delete last character
                if (text.length())
                    text = text.substring(0, text.length() - 1);
                bRedraw = true;
                break;
            case BTN_B0_LONG: // clear the text
                text.clear();
                bRedraw = true;
                break;
            case BTN_LONG:
                done = true;
                break;
            }
        } while (!done);
        // copy the string back, we already checked to make sure not too long
        strcpy(str, text.c_str());
    }
}

// scan for networks
int ScanForNetworks()
{
    // Serial.println("scan start");
    WiFi.disconnect();
    // WiFi.scanNetworks will return the number of networks found
    int retval = WiFi.scanNetworks();
    // Serial.println("scan done");
    if (retval == 0)
    {
        Serial.println("no networks found");
    }
    else
    {
        Serial.print(retval);
        Serial.println(" networks found");
        for (int i = 0; i < retval; ++i)
        {
            // Print SSID and RSSI for each network found
            Serial.print(i + 1);
            Serial.print(": ");
            Serial.print(WiFi.SSID(i));
            Serial.print(" (");
            Serial.print(WiFi.RSSI(i));
            Serial.print(")");
            Serial.println((WiFi.encryptionType(i) == WIFI_AUTH_OPEN) ? " " : "*");
        }
    }
    return retval;
}

//// display the USB voltage
// void ShowUsbVoltage(MenuItem* menu)
//{
//	ClearScreen();
//	DisplayLine(nMenuLineCount - 1, "Click/Dial=Cancel", SystemInfo.menuTextColor);
//	CRotaryDialButton::Button button = BTN_NONE;
//	bool done = false;
//	do {
//		float bat = GetUsbVoltage();
//		String str;
//		str = String("Voltage: ") + bat;
//		DisplayLine(0, str);
//		button = ReadButton();
//		switch (button) {
//		case BTN_NONE:
//			break;
//		case BTN_B1_CLICK:
//		case BTN_B2_LONG:
//		case BTN_B1_LONG:
//		case BTN_B0_CLICK:
//		case BTN_B0_LONG:
//		case BTN_RIGHT:
//		case BTN_SELECT:
//			// anything cancels
//			done = true;
//			break;
//		}
//		vTaskDelay(pdMS_TO_TICKS(500));
//	} while (!done);
// }

// get an audio file from the SD card
void GetAudioFile(MenuItem *menu)
{
    std::vector<String> extensions = {"TXT", "WAV", "MP3"};
    char *str = (char *)menu->value;
    // keep the files here
    std::vector<String> FileNames;
    // read all the filenames
    bool bAdd = false;
    for (String ext : extensions)
    {
        GetFileNamesFromSD(FileNames, bAdd, ext);
        bAdd = true;
    }
    if (str)
    {
        // holds the current selection
        int nNameIndex = 0;
        // holds the list starting index
        int nStartIndex = 0;
        String text = str;
        // find the current audio file and set the index
        int foundIx = 0;
        for (String fn : FileNames)
        {
            String to = str;
            to.toUpperCase();
            fn.toUpperCase();
            if (fn.compareTo(to) == 0)
            {
                // Serial.print(fn + " " + foundIx + "\n");
                //  set the current index and start if necessary
                nNameIndex = foundIx;
                if (foundIx >= nMenuLineCount - 1)
                {
                    nStartIndex = nNameIndex - nMenuLineCount + 2;
                }
                break;
            }
            ++foundIx;
        }
        ClearScreen();
        DisplayLine(nMenuLineCount - 1, "Long=OK Click=Cancel", SystemInfo.menuTextColor);
        CRotaryDialButton::Button button = BTN_NONE;
        bool done = false;
        // redraw screen only when necessary
        bool bRedraw = true;
        do
        {
            if (bRedraw)
            {
                String line;
                bool hilite;
                for (int ix = 0; ix < FileNames.size() && ix < nMenuLineCount - 1; ++ix)
                {
                    // highlight the current selection
                    hilite = (nNameIndex - nStartIndex) == ix;
                    line = FileNames[ix + nStartIndex];
                    if (SystemInfo.bMenuStar)
                    {
                        line = (hilite ? "*" : " ") + line;
                        DisplayLine(ix, line, SystemInfo.menuTextColor);
                    }
                    else
                    {
                        DisplayLine(ix, line, hilite ? TFT_BLACK : SystemInfo.menuTextColor, hilite ? SystemInfo.menuHiLiteColor : TFT_BLACK);
                    }
                }
                bRedraw = false;
            }
            button = ReadButton();
            switch (button)
            {
            case BTN_NONE:
            case BTN_B1_CLICK:
            case BTN_B2_LONG:
            case BTN_B1_LONG:
            case BTN_B0_CLICK:
            case BTN_B0_LONG:
                break;
            case BTN_LEFT: // previous line
                if (nNameIndex > 0)
                {
                    // select the previous one
                    --nNameIndex;
                    // check if we need to scroll
                    if (nNameIndex - nStartIndex < 0)
                    {
                        --nStartIndex;
                    }
                    bRedraw = true;
                }
                break;
            case BTN_RIGHT: // next line
                // check if more available
                if (nNameIndex < FileNames.size() - 1)
                {
                    ++nNameIndex;
                    // check if we need to scroll
                    if (nNameIndex - nStartIndex >= nMenuLineCount - 1)
                    {
                        ++nStartIndex;
                    }
                    bRedraw = true;
                }
                break;
            case BTN_LONG: // set the new name
                text = FileNames[nNameIndex];
                done = true;
                break;
            case BTN_SELECT: // use this to cancel
                done = true;
                break;
            }
        } while (!done);
        // copy the string back
        if (text.length())
            strcpy(str, text.c_str());
    }
}

// toggle web server running, reboot if needed
void ToggleWebServer(MenuItem *menu)
{
    // save existing value
    bool bWas = *(bool *)menu->value;
    ToggleBool(menu);
    bControllerReboot = (bWas != *(bool *)menu->value);
}

// cancel the radio wait timers
void CancelWaitTimers(MenuItem *)
{
    xEventGroupSetBits(gRadioEventsHandle, RadioEventCancelWaits);
}

// display a received character on the bottom line
void DisplayBottomChar(char ch)
{
    if (!g_bSettingsMode)
    {
        if (xSemaphoreTake(MutexDisplayHandle, portMAX_DELAY) == pdTRUE)
        {
            tft.setTextColor(TFT_GREEN);
            tft.setTextSize(2);
            // add ' ' to ensure spot is cleared for shorter letters like 'l'
            tft.drawString(String(ch) + ' ', tft.width() / 4, tft.height() - 16);
            tft.setTextSize(1);
            xSemaphoreGive(MutexDisplayHandle);
        }
    }
}

// map a menuitem list to html
// recurses for each eIf
String MenuToHtml(MenuItem *pMenu, bool bActive, int nLevel)
{
    static String str;
    static int ix;
    static MenuItem *menu, *StartMenu;
    static String line, name, stmp;
    double sfloat;
    if (nLevel == 0)
    {
        StartMenu = pMenu;
        str = "";
        ix = 0;
    }
    else
    {
        ++ix;
    }
    for (menu = &StartMenu[ix]; menu->op != eTerminate; ++ix, ++menu)
    {
        if (!bActive)
        {
            // skip if not one of the if else parts when not active
            switch (menu->op)
            {
            case eIfEqual:
            case eIfIntEqual:
            case eElse:
            case eEndif:
                break;
            default:
                continue;
                break;
            }
        }
        name = "bi_" + String(ix);
        // Serial.println("name: " + name);
        //  keep the line without %x's
        line = menu->text;
        if (line.indexOf("%d.%d") >= 0)
        {
            line.remove(line.indexOf("%d.%d"), 5);
        }
        while (line.indexOf('%') >= 0)
        {
            line.remove(line.indexOf('%'), 2);
        }
        switch (menu->op)
        {
        case eText:
        case eEditText:
            // case eChooseFile:
            str += String("<p>") + line + "</p>";
            break;
        case eTextFloat:
            // TODO handle floats
            break;
        case eTextInt:
            str += "<label>" + line;
            stmp = String(*(int *)(menu->value));
            sfloat = stmp.toDouble() / pow10(menu->decimals);
            stmp = String(sfloat, menu->decimals);
            str += "<input type='text' name='" + name + "' size='" + String(5) + "' value='" + stmp + "'>";
            str += "</label>";
            break;
        case eBool: // show the two text choices in (...)
            str += "<label>" + line + " (" + menu->on + "&#x2611; | " + menu->off + "&#9633;)";
            str += "<input type='checkbox' name='" + name + "' value='" + name + "'";
            if (*(bool *)(menu->value))
                str += " checked='checked'";
            str += ">";
            str += "</label>";
            break;
        case eList: // a dropdown list
            str += "<label>" + line;
            str += "<select name='" + name + "'>";
            for (int ix = 0; ix <= menu->max; ++ix)
            {
                str += "<option ";
                if (ix == *(int *)(menu->value))
                    str += "selected='" + String(ix) + "' ";
                str += "<value='" + String(ix) + "'>" + menu->nameList[ix] + "</option>";
            }
            str += "</select>";
            str += "</label>";
            break;
        case eExit:
            break;
        case eIfEqual:
            MenuToHtml(NULL, *(bool *)(menu->value) == (menu->min ? true : false), nLevel + 1);
            continue;
            break;
        case eIfIntEqual:
            MenuToHtml(NULL, *(int *)(menu->value) == (menu->min), nLevel + 1);
            continue;
            break;
        case eElse:
            bActive = !bActive;
            break;
        case eEndif:
            return str;
            break;
        case eMenu:
        case eReboot:
        case eTerminate:
            // Serial.println("unsupported menutype to html: " + String(menu->op));
            break;
        default:
            break;
        }
        if (bActive)
        {
            str += "<br>";
        }
    }
    return str;
}

// read the files from the card
void GetFileNamesFromSD(std::vector<String> &FileNames, bool bAppend, String ext, String dir)
{
    setupSDcard();
    ext.toUpperCase();
    ext = "." + ext;
    bool worked = true;
    // Serial.print("reading files: " + dir + "*" + ext);
    //  start over
    //  first empty the current file names if not appending
    if (!bAppend)
    {
        FileNames.clear();
    }
    if (dir.length() > 1)
        dir = dir.substring(0, dir.length() - 1);
    File root = SD.open(dir);
    File file;
    String CurrentFilename = "";
    if (!root)
    {
        // Serial.println("Failed to open directory: " + dir + "\n");
        worked = false;
    }
    if (!root.isDirectory())
    {
        // Serial.println("Not a directory: " + dir);
        worked = false;
    }
    if (worked)
    {
        file = root.openNextFile();
        if (dir != "/")
        {
            // add an arrow to go back
            // String sdir = currentFolder.substring(0, currentFolder.length() - 1);
            // sdir = sdir.substring(0, sdir.lastIndexOf("/"));
            // if (sdir.length() == 0)
            //	sdir = "/";
            // FileNames.push_back(String(PREVIOUS_FOLDER_CHAR));
        }
        while (file)
        {
            CurrentFilename = file.name();
            // strip path
            CurrentFilename = CurrentFilename.substring(CurrentFilename.lastIndexOf('/') + 1);
            // Serial.println("name: " + CurrentFilename);
            if (CurrentFilename != "System Volume Information")
            {
                if (file.isDirectory())
                {
                    // FileNames.push_back(String(NEXT_FOLDER_CHAR) + CurrentFilename);
                }
                else
                {
                    String uppername = CurrentFilename;
                    uppername.toUpperCase();
                    // find files with our extension only
                    if (uppername.endsWith(ext))
                    {
                        // Serial.println("name: " + CurrentFilename);
                        FileNames.push_back(CurrentFilename);
                    }
                }
            }
            file.close();
            file = root.openNextFile();
        }
        root.close();
        std::sort(FileNames.begin(), FileNames.end(), CompareNames);
        bSdCardValid = true;
    }
    else
    {
        bSdCardValid = false;
    }
    return;
}

// delete saved settings, except for the battery values
void FactorySettings(MenuItem *menu)
{
    if (menu == NULL || GetYesNo("Reset All Settings? (reboot)"))
    {
        SaveLoadBatterySettings(false);
        Preferences prefs;
        prefs.begin(prefsName);
        prefs.clear();
        prefs.end();
        SaveLoadBatterySettings(true);
        if (menu != NULL)
            ESP.restart();
    }
}

void EraseFlash(MenuItem *menu)
{
    if (GetYesNo("Format EEPROM? (factory)"))
    {
        nvs_flash_erase(); // erase the NVS partition and...
        nvs_flash_init();  // initialize the NVS partition.
    }
}

//// get USB voltage on TTGO
// float GetUsbVoltage()
//{
//	//analogSetPinAttenuation(digitalPinToDacChannel(6), ADC_0db);
//	//analogReadResolution(12);
//	//float measurement = analogReadMilliVolts(6);
//	//float voltage = (measurement / 4095.0) * 7.26;
//	//return voltage;
//	uint16_t v1 = analogRead(34);
//	uint16_t v2 = analogRead(14);
//
//	float battery_voltage = ((float)v1 / 4095.0) * 2.0 * 3.3 * (1100 / 1000.0);
//	float other_voltage = ((float)v2 / 4095.0) * 2.0 * 3.3 * (1100 / 1000.0);
//	//return other_voltage;
//	return battery_voltage;
// }

void setupSDcard()
{
    bool bSdCardValid = false;
    // see if the card is there, I.E. already initialized
    if (bSdCardValid)
        return;
    gpio_set_direction((gpio_num_t)SDcsPin, GPIO_MODE_OUTPUT);
    delay(50);
    // SPIClass(1);
    spiSDCard.begin(SDSckPin, SDMisoPin, SDMosiPin, SDcsPin); // SCK,MISO,MOSI,CS
    delay(20);

    if (!SD.begin(SDcsPin, spiSDCard))
    {
        // Serial.println("Card Mount Failed");
        return;
    }
    uint8_t cardType = SD.cardType();

    if (cardType == CARD_NONE)
    {
        // Serial.println("No SD card attached");
        return;
    }
}

// save/load battery settings
bool SaveLoadBatterySettings(bool save)
{
    bool retvalue = true;
    Preferences prefs;
    prefs.begin(prefsName, !save);
    if (save)
    {
        // save things
        prefs.putBytes(prefsBatteryInfo, &BatteryInfo, sizeof(BatteryInfo));
    }
    else
    {
        // load things
        if (prefs.getBytes(prefsBatteryInfo, &BatteryInfo, sizeof(BatteryInfo)) != sizeof(BatteryInfo))
        {
            retvalue = false;
        }
    }
    prefs.end();
    return retvalue;
}

// save/load settings
// return false if not found or wrong version
bool SaveLoadSettings(bool save, bool nodisplay)
{
    bool retvalue = true;
    Preferences prefs;
    prefs.begin(prefsName, !save);
    if (save)
    {
        // save things
        prefs.putString(prefsVersion, FOX_Version);
        prefs.putBytes(prefsSystemInfo, &SystemInfo, sizeof(SystemInfo));
        if (!nodisplay)
        {
            WriteMessage("Settings Saved", false, 1000);
        }
    }
    else
    {
        // load things
        String vsn = prefs.getString(prefsVersion, "");
        if (vsn == FOX_Version)
        {
            setupSDcard();
            // set the brightness values since they might have changed
            SetDisplayBrightness(SystemInfo.nDisplayBrightness);
            prefs.getBytes(prefsSystemInfo, &SystemInfo, sizeof(SystemInfo));
            if (!nodisplay)
            {
                WriteMessage("Settings Loaded", false, 1000);
            }
        }
        else
        {
            retvalue = false;
            if (!nodisplay)
                WriteMessage("Settings not saved yet", true, 2000);
        }
    }
    prefs.end();
    // always do the battery ones
    SaveLoadBatterySettings(save);
    return retvalue;
}

// check buttons and return if one pressed
// check the rotation buttons during running
enum CRotaryDialButton::Button ReadButton()
{
    if (SystemInfo.bRunWebServer)
    {
        server.handleClient();
    }
    enum CRotaryDialButton::Button retValue = BTN_NONE;
    // read the next button, or NONE if none there
    retValue = CRotaryDialButton::dequeue();
    // reboot?
    if (retValue == BTN_B2_LONG)
        ESP.restart();
    // if no buttons, yield so other tasks get to run
    if (retValue == BTN_NONE)
        vTaskDelay(pdMS_TO_TICKS(2));
    // turn the b1 button into a dial long click
    if (retValue == BTN_B1_CLICK)
        retValue = BTN_LONG;
    if (retValue != BTN_NONE)
    {
        ResetDimTimer();
    }
    else if (displayDimNow)
    {
        for (int val = SystemInfo.nDisplayBrightness - 1; val >= SystemInfo.nDisplayDimValue; --val)
        {
            SetDisplayBrightness(val);
            if (CRotaryDialButton::getCount())
            {
                // if button pressed finish and get out of here
                SetDisplayBrightness(SystemInfo.nDisplayBrightness);
                break;
            }
            delay(10);
        }
        displayDimNow = false;
    }
    return retValue;
}

// just check for longpress and cancel if it was there
bool CheckCancel(bool bLeaveButton)
{
    ResetDimTimer();
    // if it has been set, just return true
    CRotaryDialButton::Button button = ReadButton();
    if (button != BTN_NONE)
    {
        if (button == BTN_LONG)
        {
            return true;
        }
        else if (bLeaveButton)
        {
            CRotaryDialButton::pushButton(button);
        }
    }
    return false;
}

// check if any important radio settings have changed between the two sets
// return true if any changes found
bool CompareRadioSettings(SYSTEM_INFO *pSystemInfo, SYSTEM_INFO *pSystemInfoSaved)
{
    bool retval = false;
#define SIVL_ENTRY(x)                                  \
    {                                                  \
        offsetof(SYSTEM_INFO, x), sizeof(SystemInfo.x) \
    }
    static struct SYSINFO_VALUE_LIST
    {
        uint offset;
        uint size;
    } sysInfoValueList[] = {
        SIVL_ENTRY(nBandWidth),
        SIVL_ENTRY(nFrequency),
        SIVL_ENTRY(nRfOffset),
        SIVL_ENTRY(nTxCTCSS),
        SIVL_ENTRY(nSquelch),
        SIVL_ENTRY(nRxCTCSS),
        SIVL_ENTRY(nRxVolume),
        SIVL_ENTRY(bCTCSS),
        SIVL_ENTRY(bTxDcsNI),
        SIVL_ENTRY(bRxDcsNI),
        SIVL_ENTRY(nTxDcs),
        SIVL_ENTRY(nRxDcs),
    };
    byte *a = (byte *)pSystemInfo;
    byte *b = (byte *)pSystemInfoSaved;
    for (struct SYSINFO_VALUE_LIST vl : sysInfoValueList)
    {
        // compare them
        if (memcmp(a + vl.offset, b + vl.offset, vl.size) != 0)
        {
            retval = true;
            break;
        }
    }
    return retval;
}

void InitMenuSystem()
{
    CRotaryDialButton::begin((gpio_num_t)DIAL_A, (gpio_num_t)DIAL_B, (gpio_num_t)DIAL_BTN, (gpio_num_t)0, (gpio_num_t)35, (gpio_num_t)-1, (gpio_num_t)-1, &SystemInfo.DialSettings);
    // we know that this is a toggle switch type on the PCB
    SystemInfo.DialSettings.m_bToggleDial = true;
    // init the onboard buttons
    gpio_set_direction(GPIO_NUM_0, GPIO_MODE_INPUT);
    gpio_set_pull_mode(GPIO_NUM_0, GPIO_PULLUP_ONLY);
    // configure LCD PWM functionality
    // attach the channel to the GPIO to be controlled
    pinMode(TFT_ENABLE, OUTPUT);
    digitalWrite(TFT_ENABLE, 1);
    ledcAttach(TFT_ENABLE, 1000, 8);
    //******
    // esp_chip_info_t data;
    // esp_chip_info(&data);
    // Serial.println(String("chip:") + data.model + " features:" + String(data.features, 2) + " cores:" + data.cores);
    // init the display
    tft.init();
    tft.fillScreen(TFT_BLACK);
    tft.setRotation(3);
    tft.setFreeFont(&Dialog_bold_16);
    tft.setTextSize(1);
    tft.setTextPadding(tft.width());
    tft.setTextColor(SystemInfo.menuTextColor);
    tft.drawString("Radio Fox Initializing...", 4, 10);
    delay(750);
    nMenuLineCount = (tft.height() + 1) / tft.fontHeight();
    TextLines.resize(nMenuLineCount);
    // create the display mutex
    MutexDisplayHandle = xSemaphoreCreateMutex();
    setupSDcard();
    SystemInfo.bCriticalBatteryLevel = false;
    SetDisplayBrightness(SystemInfo.nDisplayBrightness);
    // see if the button is down, if so clear all settings
    if (gpio_get_level((gpio_num_t)DIAL_BTN) == 0)
    {
        FactorySettings(NULL);
        tft.fillScreen(TFT_BLACK);
        WriteMessage("Factory Reset");
        delay(2000);
    }
    String msg;
    // see if we can read the settings
    if (SaveLoadSettings(false, true))
    {
        msg = "Settings Loaded";
    }
    else
    {
        // must not be anything there, so save it
        SaveLoadSettings(true, false);
    }
    SetDisplayBrightness(SystemInfo.nDisplayBrightness);
#if !HAS_BATTERY_LEVEL
    SystemInfo.bShowBatteryLevel = false;
#endif
    // get our text line sprite ready
    LineSprite.setColorDepth(16);
    LineSprite.createSprite(tft.width(), tft.fontHeight());
    LineSprite.fillSprite(TFT_BLACK);
    LineSprite.setFreeFont(&Dialog_bold_16);
    LineSprite.setTextPadding(tft.width());
    // get our Battery sprite ready
    BatterySprite.setColorDepth(16);
    // TODO fix this so it will work with a width other than 100, needs code change also
    BatterySprite.createSprite(100, tft.fontHeight() + BATTERY_BAR_HEIGHT);
    BatterySprite.fillSprite(TFT_BLACK);
    BatterySprite.setFreeFont(&Dialog_bold_16);
    BatterySprite.setTextPadding(tft.width());
    // get the menu system ready
    menuPtr = new MenuInfo;
    MenuStack.push(menuPtr);
    MenuStack.top()->menu = MainMenu;
    MenuStack.top()->index = 0;
    MenuStack.top()->offset = 0;
    tft.fillScreen(TFT_BLACK);
    tft.setTextColor(SystemInfo.menuTextColor);
    tft.setTextColor(TFT_BLUE);
    tft.setFreeFont(&Irish_Grover_Regular_24);
    tft.drawRect(0, 0, tft.width() - 1, tft.height() - 1, SystemInfo.menuTextColor);
    tft.drawRect(1, 1, tft.width() - 2, tft.height() - 2, SystemInfo.menuTextColor);
    tft.drawString("Radio Fox", 60, 10);
    tft.setFreeFont(&Dialog_bold_16);
    tft.drawString(String("Version ") + FOX_Version, 20, 70);
    tft.setTextSize(1);
    tft.drawString(__DATE__, 20, 90);
    if (msg.length())
    {
        tft.drawString(msg, 20, 110);
    }
    // clear the button buffer
    CRotaryDialButton::clear();
    delay(3000);
    ClearScreen();
}
#if 0 // not used, but might be useful later
String file_size(int bytes)
{
    String fsize = "";
    if (bytes < 1024)
        fsize = String(bytes) + " B";
    else if (bytes < (1024 * 1024))
        fsize = String(bytes / 1024.0, 3) + " KB";
    else if (bytes < (1024 * 1024 * 1024))
        fsize = String(bytes / 1024.0 / 1024.0, 3) + " MB";
    else
        fsize = String(bytes / 1024.0 / 1024.0 / 1024.0, 3) + " GB";
    return fsize;
}
#endif
