MartinNohr/RadioFox/include/FoxServer.h

#pragma once
void InitServer();
void load_page_header(bool bRefresh);
void HomePage();
void append_page_footer();
void SendHTML_Header();
void SendHTML_Content();
void SendHTML_Stop();
void WebChangeSettings();
void WebShowSettings();
void UtilitiesPage();
void VerifyRebootSystem();
void RebootSystem();
